Shirnish/esp32-room-environment-monitor/HardWare/room-environment-monitor-v2-current/room-environment-monitor-v2-current.kicad_sch

## KiCad design HardWare/room-environment-monitor-v2-current/room-environment-monitor-v2-current.kicad_sch (2026-10-04)

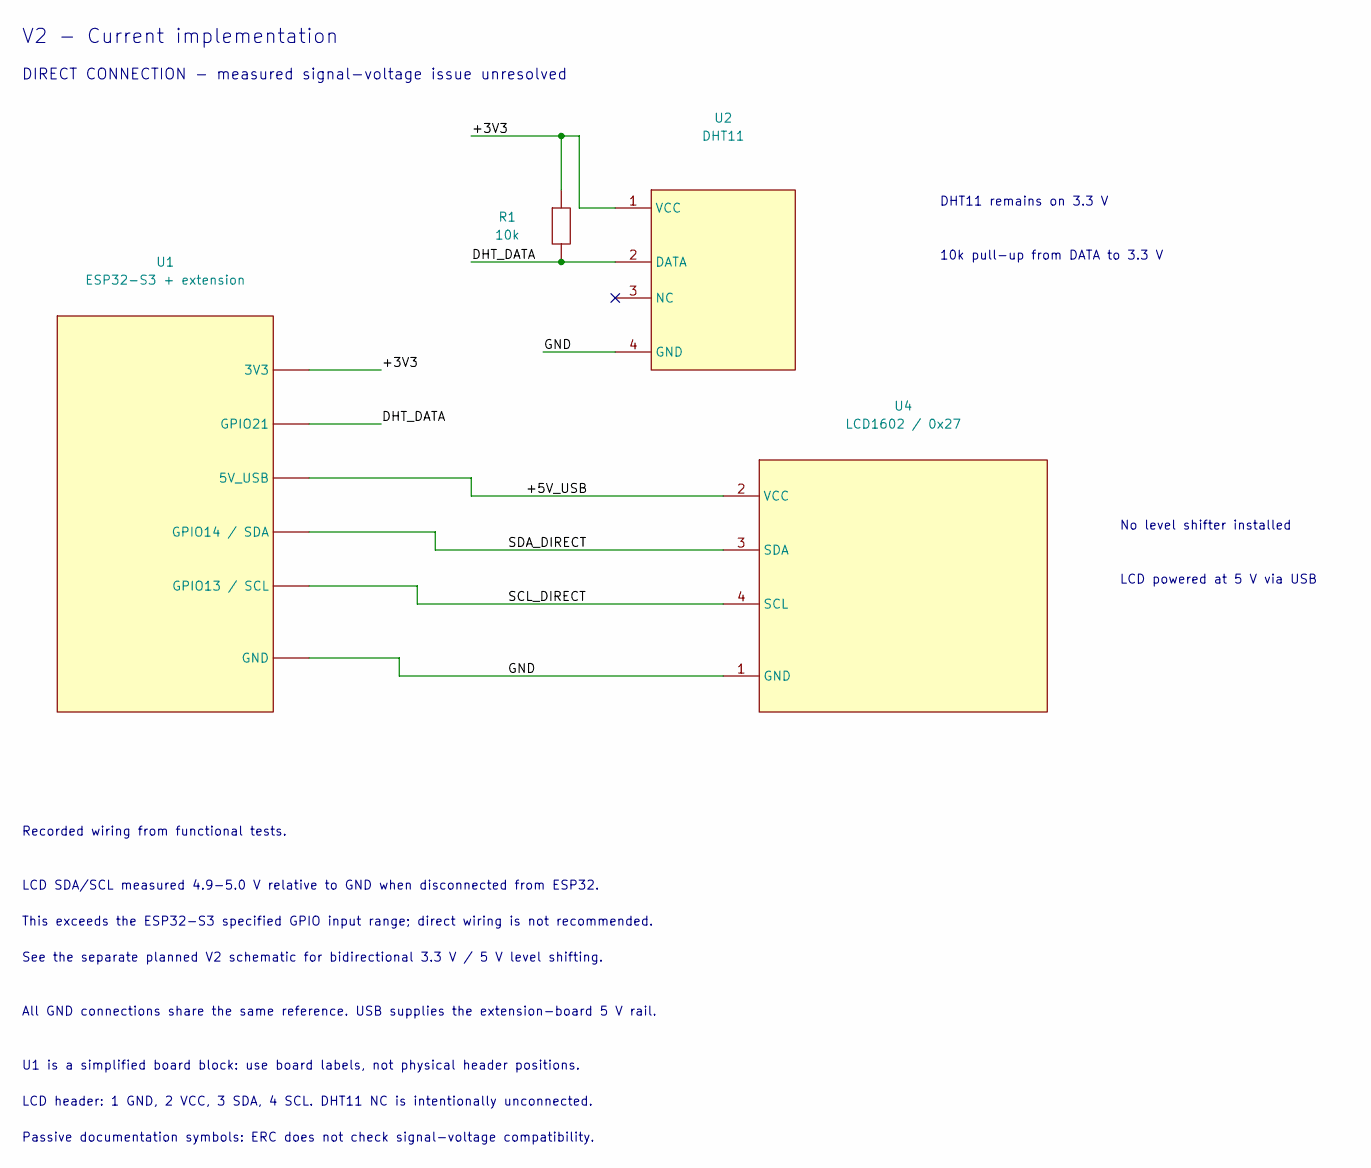
[picture p6: schematic room-environment-monitor-v2-current.kicad_sch]

Parts:
R1: 10k
U1: ESP32-S3 + extension
U2: DHT11
U4: LCD1602 / 0x27

Connections:
+3V3: R1.1, U1.3V3, U2.1 (VCC)
+5V_USB: U1.5V (5V_USB), U4.2 (VCC)
DHT_DATA: R1.2, U1.GPIO21, U2.2 (DATA)
GND: U1.GND, U2.4 (GND), U4.1 (GND)
SCL_DIRECT: U1.GPIO13 (GPIO13 / SCL), U4.4 (SCL)
SDA_DIRECT: U1.GPIO14 (GPIO14 / SDA), U4.3 (SDA)

Notes on the sheet:
V2 - Current implementation
DIRECT CONNECTION - measured signal-voltage issue unresolved
DHT11 remains on 3.3 V
10k pull-up from DATA to 3.3 V
No level shifter installed
LCD powered at 5 V via USB
Recorded wiring from functional tests.
LCD SDA/SCL measured 4.9-5.0 V relative to GND when disconnected from ESP32.
This exceeds the ESP32-S3 specified GPIO input range; direct wiring is not recommended.
See the separate planned V2 schematic for bidirectional 3.3 V / 5 V level shifting.
All GND connections share the same reference. USB supplies the extension-board 5 V rail.
U1 is a simplified board block: use board labels, not physical header positions.
LCD header: 1 GND, 2 VCC, 3 SDA, 4 SCL. DHT11 NC is intentionally unconnected.
Passive documentation symbols: ERC does not check signal-voltage compatibility.
