Shirnish/esp32-room-environment-monitor/HardWare/room-environment-monitor-v2/room-environment-monitor-v2.kicad_sch

## KiCad design HardWare/room-environment-monitor-v2/room-environment-monitor-v2.kicad_sch (2026-10-04)

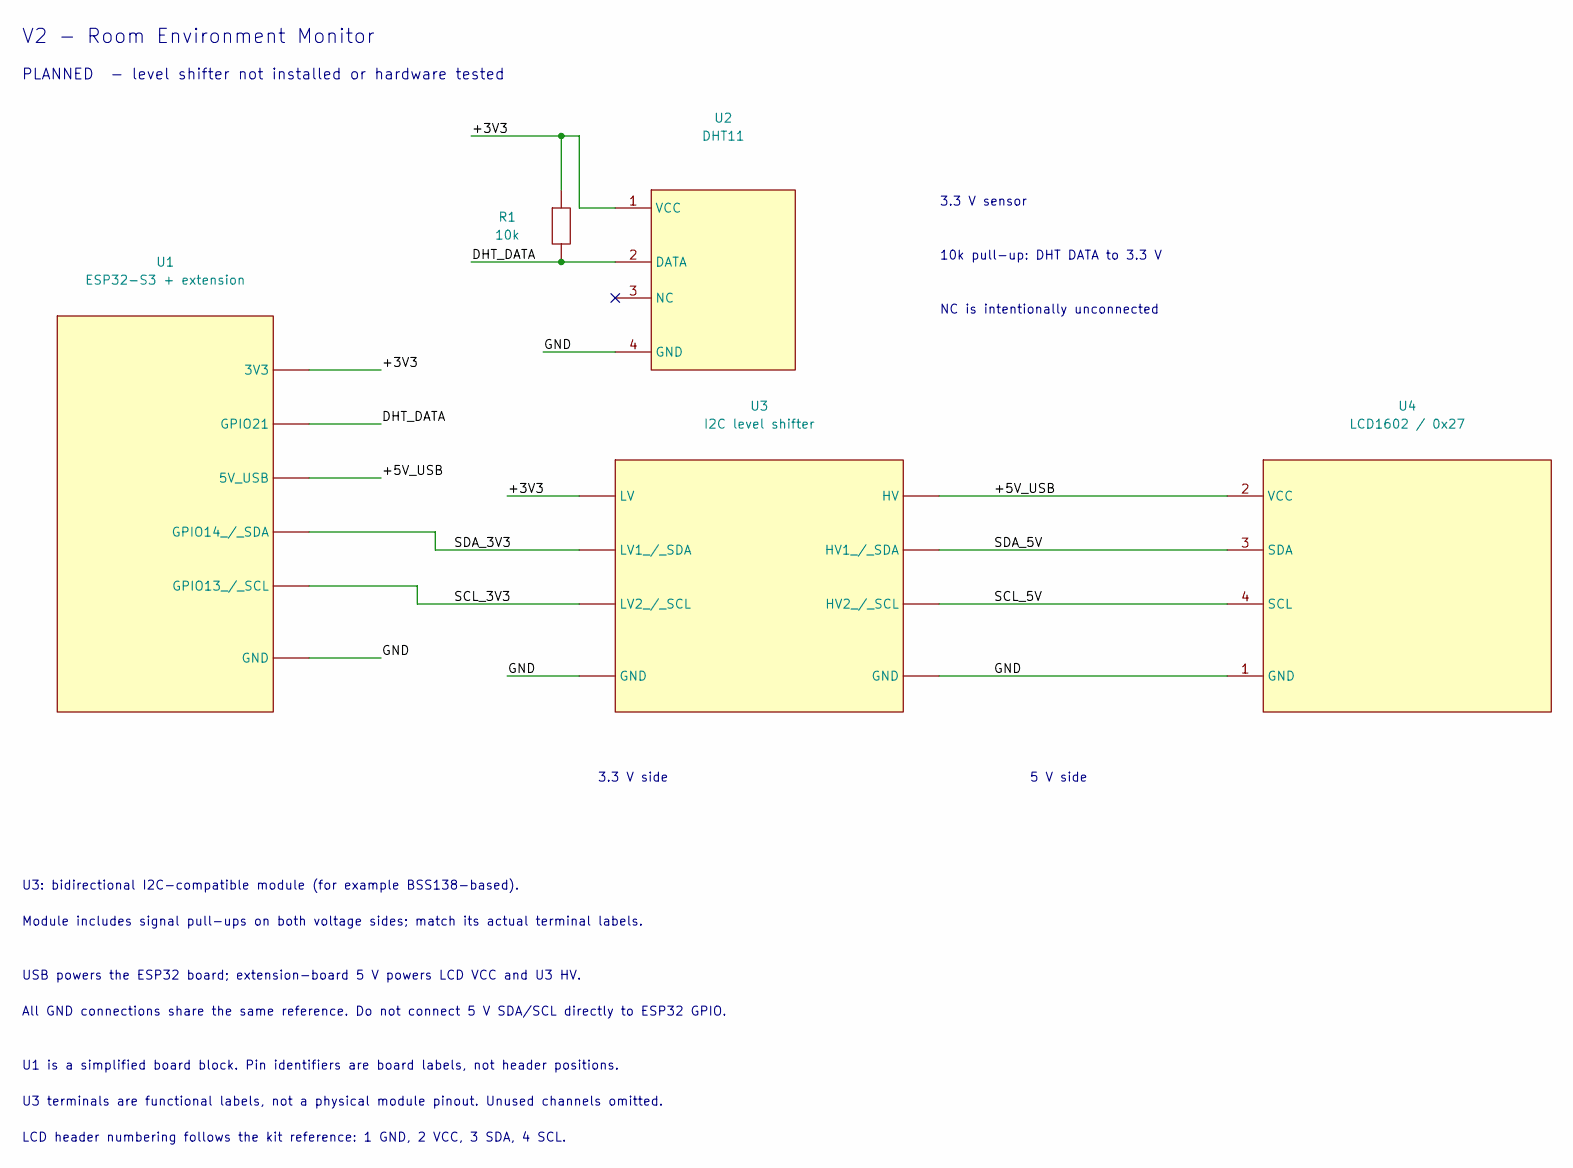
[picture p7: schematic room-environment-monitor-v2.kicad_sch]

Parts:
R1: 10k
U1: ESP32-S3 + extension
U2: DHT11
U3: I2C level shifter
U4: LCD1602 / 0x27

Connections:
+3V3: R1.1, U1.3V3, U2.1 (VCC), U3.LV
+5V_USB: U1.5V (5V_USB), U3.HV, U4.2 (VCC)
DHT_DATA: R1.2, U1.GPIO21, U2.2 (DATA)
GND: U1.GND, U2.4 (GND), U3.GND_H (GND), U3.GND_L (GND), U4.1 (GND)
SCL_3V3: U1.GPIO13 (GPIO13_/_SCL), U3.LV2 (LV2_/_SCL)
SCL_5V: U3.HV2 (HV2_/_SCL), U4.4 (SCL)
SDA_3V3: U1.GPIO14 (GPIO14_/_SDA), U3.LV1 (LV1_/_SDA)
SDA_5V: U3.HV1 (HV1_/_SDA), U4.3 (SDA)

Notes on the sheet:
U3: bidirectional I2C-compatible module (for example BSS138-based).
NC is intentionally unconnected
U3 terminals are functional labels, not a physical module pinout. Unused channels omitted.
LCD header numbering follows the kit reference: 1 GND, 2 VCC, 3 SDA, 4 SCL.
3.3 V sensor
U1 is a simplified board block. Pin identifiers are board labels, not header positions.
Module includes signal pull-ups on both voltage sides; match its actual terminal labels.
V2 - Room Environment Monitor
3.3 V side
USB powers the ESP32 board; extension-board 5 V powers LCD VCC and U3 HV.
5 V side
PLANNED - level shifter not installed or hardware tested
All GND connections share the same reference. Do not connect 5 V SDA/SCL directly to ESP32 GPIO.
10k pull-up: DHT DATA to 3.3 V
